PanditAdityaJi/CLASSD-AMP/LTSPICECLASSD/CLASS D.asc

C1: cap; 10nF
C2: cap; 1nF
C3: cap; 10nF
C4: cap; 10nF
C5: cap; 0.47µF
C6: cap; 0.47µF
L1: ind; 33µH; Rser=1m
M1: pmos
M2: nmos
Q1: npn
Q2: pnp
R1: res; 100k
R2: res; 100k
R3: res; 1k
R4: res; 3.3k
R5: res; 1k
R6: res; 100
R7: res; 8
R8: res; 100k
U1: NE555
U2: UniversalOpAmp2
V1: voltage; SINE(0 0.5 1k)
V2: voltage; 12
V3: voltage; 24
Named nets: 0, TRIANGLE, GATE, Switching, AUDIO_OUT
.tran 20m
We are getting audio output
Now we will check on what LC filter done to minimize
BLUE ONE IS ALSO OUTPUT BUT WITHOUT FILTER
GREEN ONE IS REFINED OUTPUT
GATE IS STABLE
TRIANGLE WAVES are not that visible
so we will cross check circuit
NOW wew are getting perfect triangular waves
AS you can can TRrangular waves are highly noisy and output also 
red are output audio
green are refined and filtered audio output
filterd cuttoff frequency in 300-400 as we wanted
1 fundamental frequency near 200khz
since our circuit is electrically workingg we will start designing in kicad
